intergalaktik/ulx4m-ls/pic/ULX4M-LD_bottom_v001.png

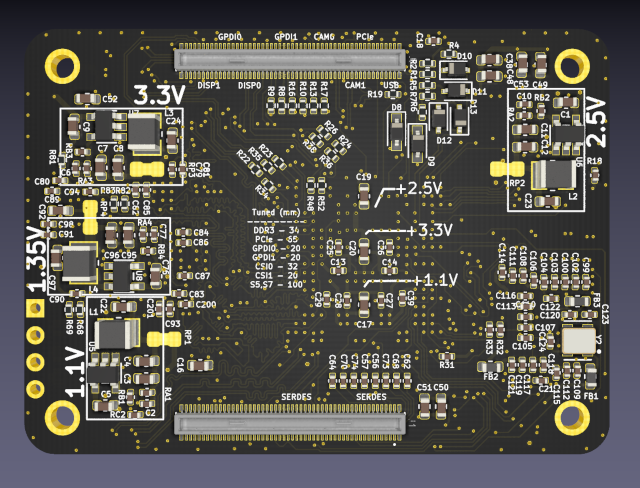
pic/ULX4M-LD_bottom_v001.png
