intergalaktik/ulx4m-ls/pic/ULX4M-LS_top_v003.png

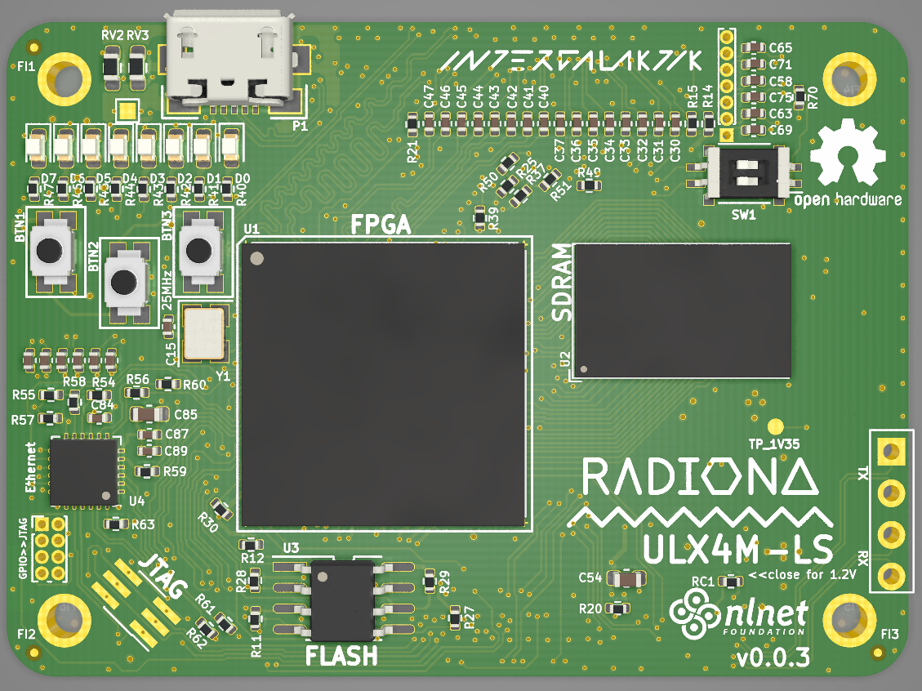
pic/ULX4M-LS_top_v003.png
