intergalaktik/ulx4m-ls/pic/ulx4m.png

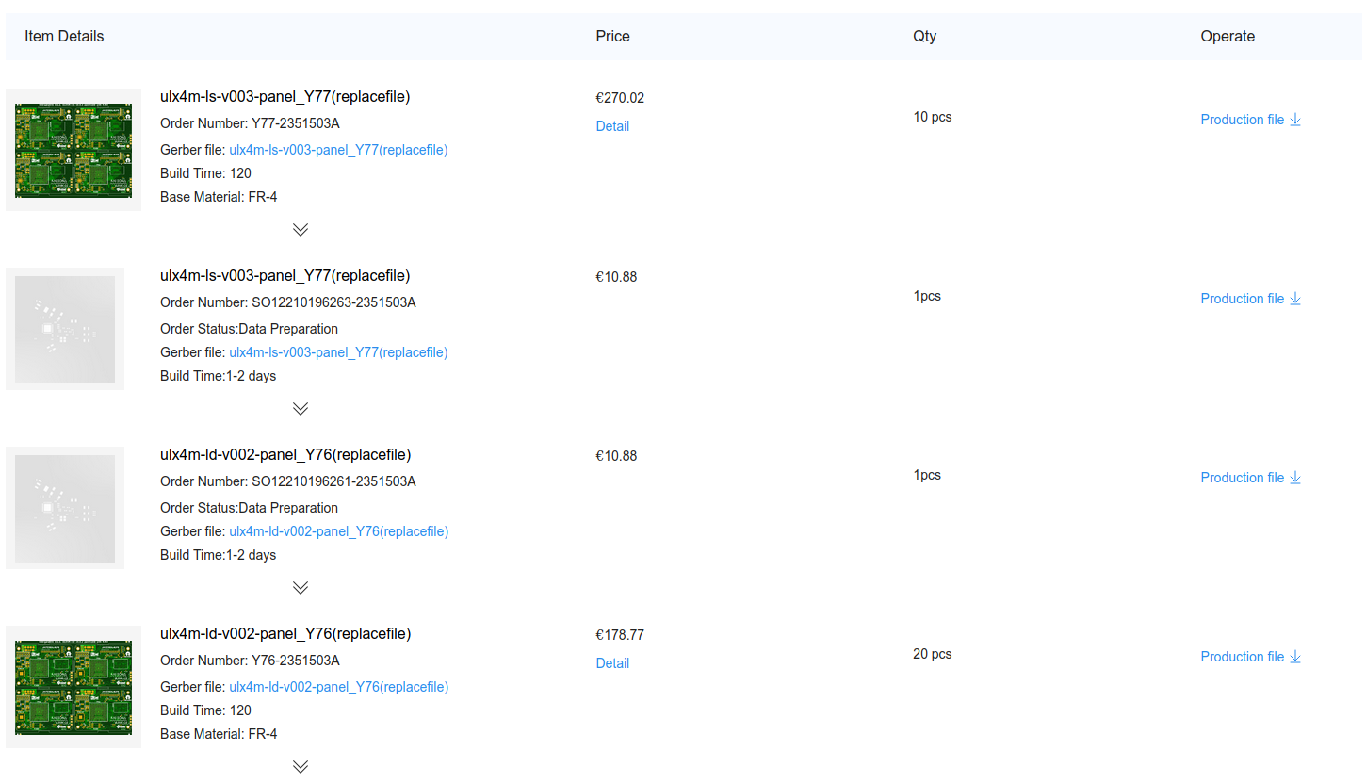
pic/ulx4m.png
