intergalaktik/ulx4m-ls/pic/ulx4m_ld_panel.png

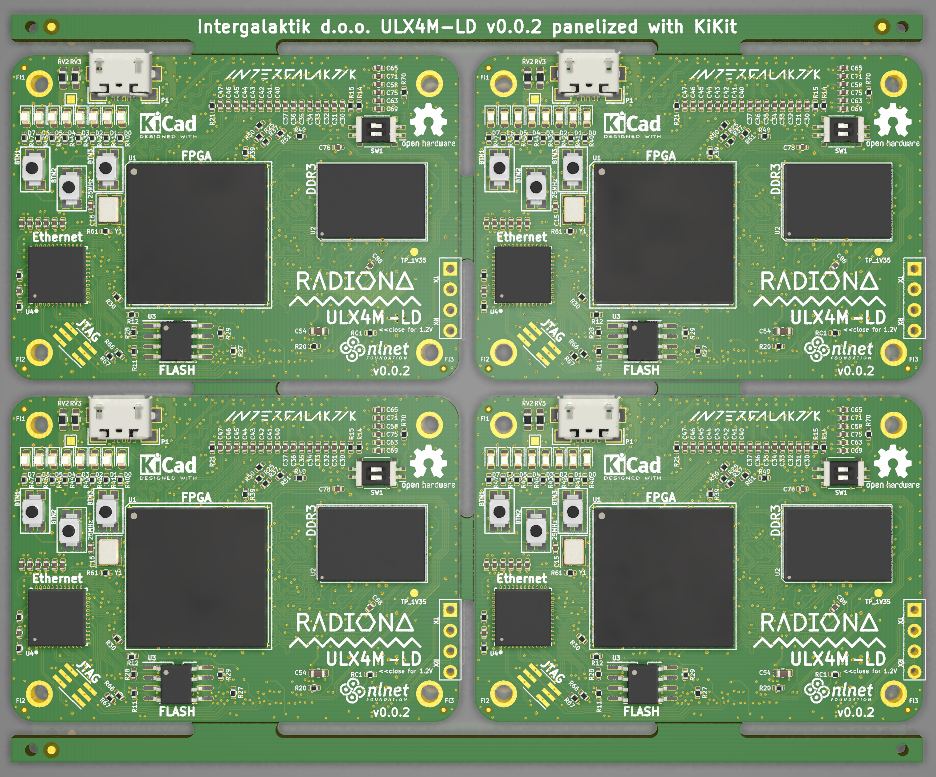
pic/ulx4m_ld_panel.png
