intergalaktik/ulx4m-ls/blinkey.kicad_sch

## KiCad design blinkey.kicad_sch (2025-04-09)

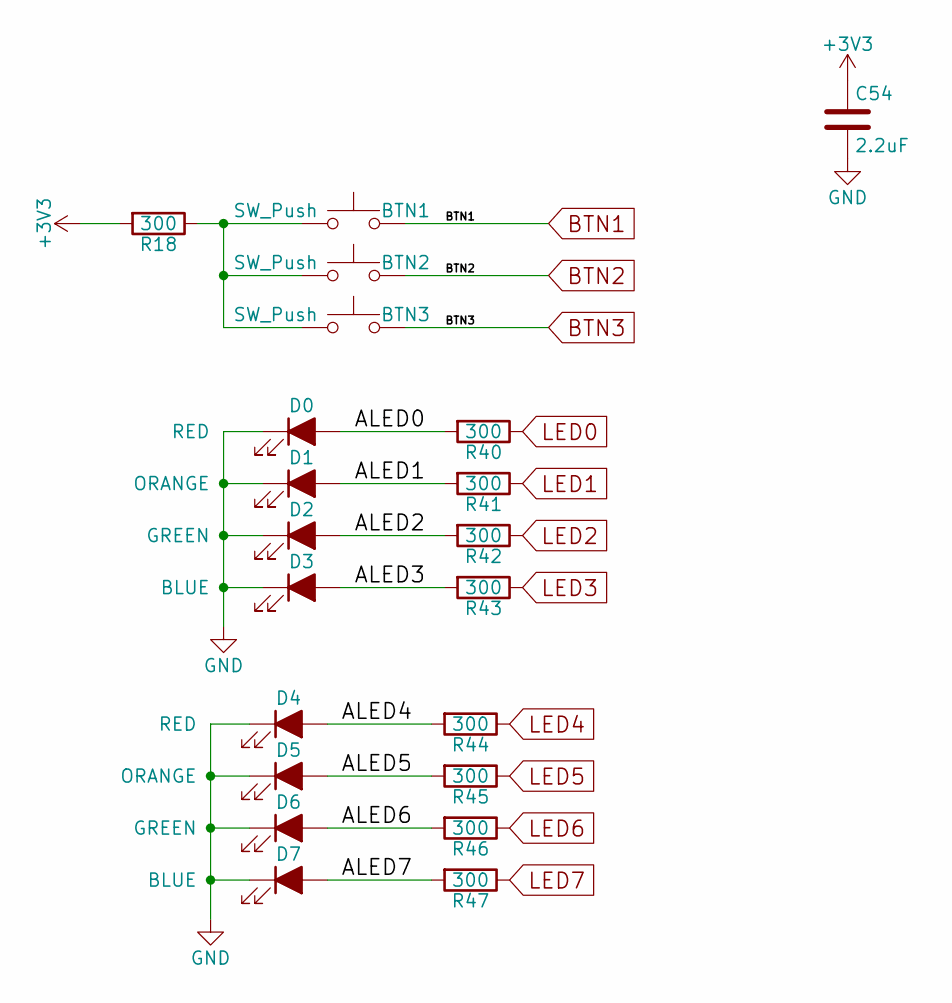
[picture p39: schematic blinkey.kicad_sch]

Parts:
BTN1, BTN2, BTN3: SW_Push; Switch_EVPAA
C54: 2.2uF; C_0603_1608Metric; MPN CC0805MRX5R6BB225
D0, D4: RED; LED_0603_1608Metric; MPN LTST-C170KRKT; Mouser 859-LTST-C170KRKT
D1, D5: ORANGE; LED_0603_1608Metric; MPN LTST-C170KFKT; Mouser 859-LTST-C170KFKT
D2, D6: GREEN; LED_0603_1608Metric; MPN LTST-C170TGKT; Mouser 859-LTST-C170TGKT
D3, D7: BLUE; LED_0603_1608Metric; MPN LTST-C170TBKT; Mouser 859-LTST-C170TBKT
R18, R40, R41, R42, R43, R44, R45, R46, R47: 300; R_0402_1005Metric

Connections:
+3V3: C54.1, R18.2
ALED0: D0.2 (A), R40.2
ALED1: D1.2 (A), R41.2
ALED2: D2.2 (A), R42.2
ALED3: D3.2 (A), R43.2
ALED4: D4.2 (A), R44.2
ALED5: D5.2 (A), R45.2
ALED6: D6.2 (A), R46.2
ALED7: D7.2 (A), R47.2
BTN1: BTN1.2
BTN2: BTN2.2
BTN3: BTN3.2
GND: C54.2, D0.1 (K), D1.1 (K), D2.1 (K), D3.1 (K), D4.1 (K), D5.1 (K), D6.1 (K), D7.1 (K)
LED0: R40.1
LED1: R41.1
LED2: R42.1
LED3: R43.1
LED4: R44.1
LED5: R45.1
LED6: R46.1
LED7: R47.1
unnamed: BTN1.1, BTN2.1, BTN3.1, R18.1
