intergalaktik/ulx4m-ls/ddr3.kicad_sch

## KiCad design ddr3.kicad_sch (2025-04-09)

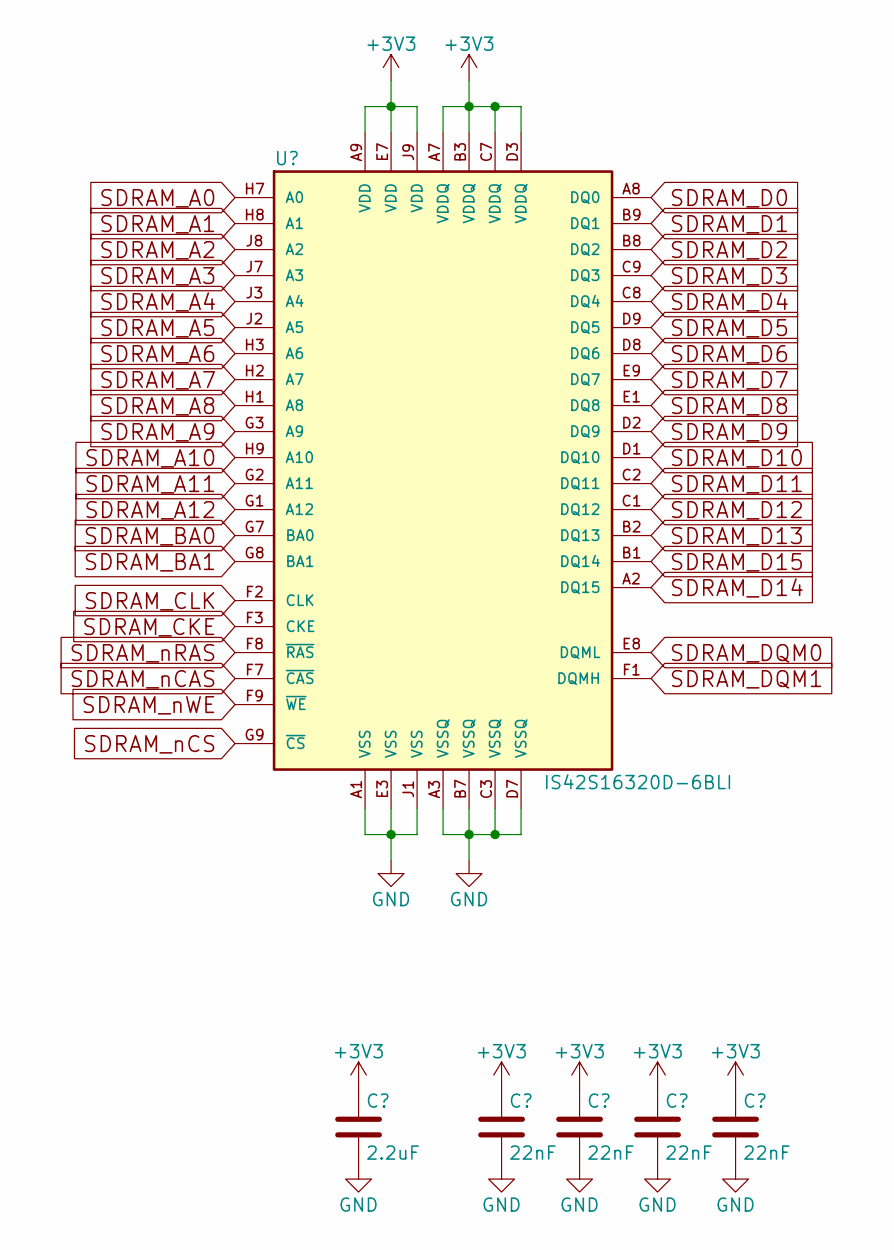
[picture p40: schematic ddr3.kicad_sch]

Parts:
C78: 2.2uF; C_0603_1608Metric
C79, C80, C81: 22nF; C_0402_1005Metric; MPN CX0603MRX7R8BB223
C82: 22nF; C_0603_1608Metric; MPN CX0603MRX7R8BB223
U2: IS42S16320D-6BLI

Connections:
+3V3: C78.1, C79.1, C80.1, C81.1, C82.1, U2.A7 (VDDQ), U2.A9 (VDD), U2.B3 (VDDQ), U2.C7 (VDDQ), U2.D3 (VDDQ), U2.E7 (VDD), U2.J9 (VDD)
GND: C78.2, C79.2, C80.2, C81.2, C82.2, U2.A1 (VSS), U2.A3 (VSSQ), U2.B7 (VSSQ), U2.C3 (VSSQ), U2.D7 (VSSQ), U2.E3 (VSS), U2.J1 (VSS)
SDRAM_A0: U2.H7 (A0)
SDRAM_A1: U2.H8 (A1)
SDRAM_A2: U2.J8 (A2)
SDRAM_A3: U2.J7 (A3)
SDRAM_A4: U2.J3 (A4)
SDRAM_A5: U2.J2 (A5)
SDRAM_A6: U2.H3 (A6)
SDRAM_A7: U2.H2 (A7)
SDRAM_A8: U2.H1 (A8)
SDRAM_A9: U2.G3 (A9)
SDRAM_A10: U2.H9 (A10)
SDRAM_A11: U2.G2 (A11)
SDRAM_A12: U2.G1 (A12)
SDRAM_BA0: U2.G7 (BA0)
SDRAM_BA1: U2.G8 (BA1)
SDRAM_CKE: U2.F3 (CKE)
SDRAM_CLK: U2.F2 (CLK)
SDRAM_D0: U2.A8 (DQ0)
SDRAM_D1: U2.B9 (DQ1)
SDRAM_D2: U2.B8 (DQ2)
SDRAM_D3: U2.C9 (DQ3)
SDRAM_D4: U2.C8 (DQ4)
SDRAM_D5: U2.D9 (DQ5)
SDRAM_D6: U2.D8 (DQ6)
SDRAM_D7: U2.E9 (DQ7)
SDRAM_D8: U2.E1 (DQ8)
SDRAM_D9: U2.D2 (DQ9)
SDRAM_D10: U2.D1 (DQ10)
SDRAM_D11: U2.C2 (DQ11)
SDRAM_D12: U2.C1 (DQ12)
SDRAM_D13: U2.B2 (DQ13)
SDRAM_D14: U2.A2 (DQ15)
SDRAM_D15: U2.B1 (DQ14)
SDRAM_DQM0: U2.E8 (DQML)
SDRAM_DQM1: U2.F1 (DQMH)
SDRAM_nCAS: U2.F7 (~CAS)
SDRAM_nCS: U2.G9 (~CS)
SDRAM_nRAS: U2.F8 (~RAS)
SDRAM_nWE: U2.F9 (~WE)
