intergalaktik/ulx4m-ls/ethernet.kicad_sch

## KiCad design ethernet.kicad_sch (2025-04-09)

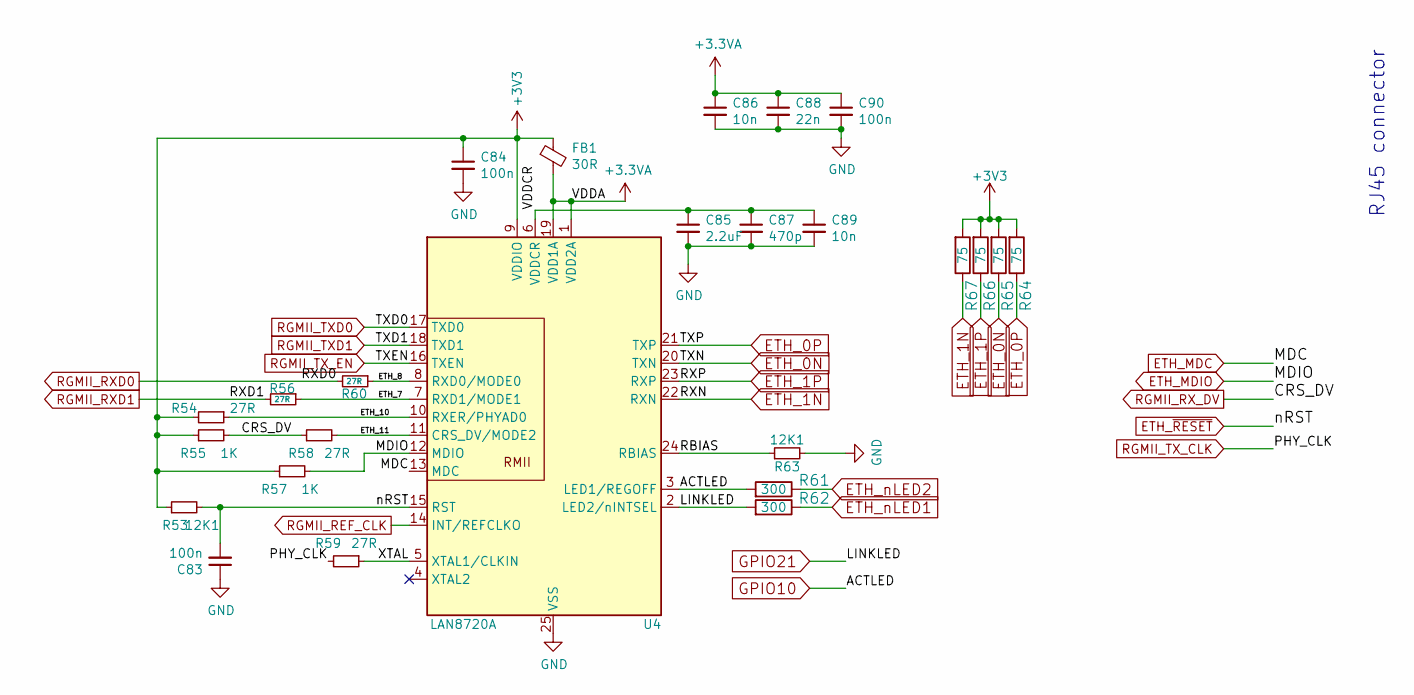
[picture p41: schematic ethernet.kicad_sch]

Parts:
C83, C84, C90: 100n; C_0402_1005Metric
C85: 2.2uF; C_0603_1608Metric
C86, C89: 10n; C_0402_1005Metric
C87: 470p; C_0402_1005Metric
C88: 22n; C_0402_1005Metric
FB1: 30R; L_0603_1608Metric
R53, R63: 12K1; R_0402_1005Metric
R54, R56, R58, R59, R60: 27R; R_0402_1005Metric
R55, R57: 1K; R_0402_1005Metric
R61, R62, R64, R65, R66, R67: 300; R_0402_1005Metric; MPN CR0402-FX-1001GLF
U4: LAN8720A; QFN-24-1EP_4x4mm_P0.5mm_EP2.6x2.6mm

Connections:
+3.3VA: C86.1, C88.1, C90.1, FB1.2, U4.1 (VDD2A), U4.19 (VDD1A)
+3V3: C84.1, FB1.1, R53.1, R54.2, R55.1, R57.1, R64.2, R65.2, R66.2, R67.2, U4.9 (VDDIO)
ETH_0N: R65.1, U4.20 (TXN)
ETH_0P: R64.1, U4.21 (TXP)
ETH_1N: R67.1, U4.22 (RXN)
ETH_1P: R66.1, U4.23 (RXP)
ETH_7: R56.1, U4.7 (RXD1/MODE1)
ETH_8: R60.1, U4.8 (RXD0/MODE0)
ETH_10: R54.1, U4.10 (RXER/PHYAD0)
ETH_11: R58.2, U4.11 (CRS_DV/MODE2)
ETH_MDC: U4.13 (MDC)
ETH_MDIO: R57.2, U4.12 (MDIO)
ETH_nLED1: R62.1
ETH_nLED2: R61.1
ETH_~RESET: C83.2, R53.2, U4.15 (RST)
GND: C83.1, C84.2, C85.2, C86.2, C87.2, C88.2, C89.2, C90.2, R63.2, U4.25 (VSS)
GPIO10: R61.2, U4.3 (LED1/REGOFF)
GPIO21: R62.2, U4.2 (LED2/nINTSEL)
RBIAS: R63.1, U4.24 (RBIAS)
RGMII_REF_CLK: U4.14 (INT/REFCLKO)
RGMII_RXD0: R60.2
RGMII_RXD1: R56.2
RGMII_RX_DV: R55.2, R58.1
RGMII_TXD0: U4.17 (TXD0)
RGMII_TXD1: U4.18 (TXD1)
RGMII_TX_CLK: R59.2
RGMII_TX_EN: U4.16 (TXEN)
VDDCR: C85.1, C87.1, C89.1, U4.6 (VDDCR)
XTAL: R59.1, U4.5 (XTAL1/CLKIN)

Notes on the sheet:
RJ45 connector
