intergalaktik/ulx4m-ls/flash.kicad_sch

## KiCad design flash.kicad_sch (2025-04-09)

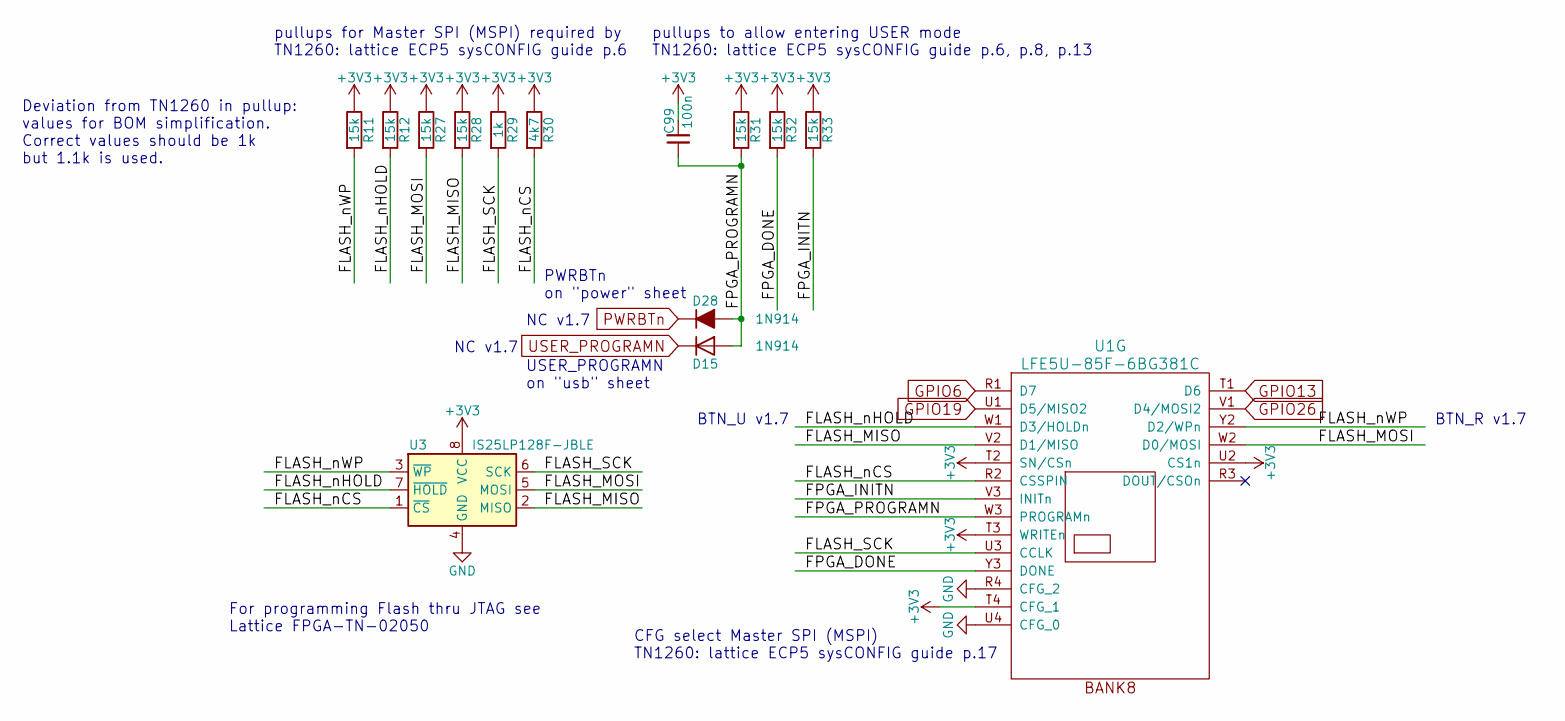
[picture p42: schematic flash.kicad_sch]

Parts:
C99: 100n; C_0402_1005Metric
D15: 1N914; D_SOD-323
D28: 1N914; D_SOD-323; Digike_y 1N4148WXTPMSCT-ND
R11: 15k; R_0402_1005Metric; MPN RC0603FR-0710KL; Mouser 603-RC0603FR-0710KL
R12, R27, R28, R31, R32, R33: 15k; R_0402_1005Metric
R29: 1k; R_0402_1005Metric
R30: 4k7; R_0402_1005Metric; MPN AC0603FR-104K7L
U1: LFE5U-85F-6BG381C; BGA-381_pitch0.8mm_dia0.4mm; MPN LFE5U-85F-6BG381C; Digike_y2 220-2071-ND
U3: IS25LP128F-JBLE; SOA008-150-208mil; MPN IS25LP128F-JBLE; Mouser 727-S25FL128LAMFV013

Connections:
+3V3: C99.2, R11.1, R12.1, R27.1, R28.1, R29.1, R30.1, R31.1, R32.1, R33.1, U1.T2 (SN/CSn), U1.T3 (WRITEn), U1.T4 (CFG_1), U1.U2 (CS1n), U3.8 (VCC)
FLASH_MISO: R28.2, U1.V2 (D1/MISO), U3.2 (MISO)
FLASH_MOSI: R27.2, U1.W2 (D0/MOSI), U3.5 (MOSI)
FLASH_SCK: R29.2, U1.U3 (CCLK), U3.6 (SCK)
FLASH_nCS: R30.2, U1.R2 (CSSPIN), U3.1 (~CS)
FLASH_nHOLD: R12.2, U1.W1 (D3/HOLDn), U3.7 (~HOLD)
FLASH_nWP: R11.2, U1.Y2 (D2/WPn), U3.3 (~WP)
FPGA_DONE: R32.2, U1.Y3 (DONE)
FPGA_INITN: R33.2, U1.V3 (INITn)
FPGA_PROGRAMN: C99.1, D15.2 (A), D28.2 (A), R31.2, U1.W3 (PROGRAMn)
GND: U1.R4 (CFG_2), U1.U4 (CFG_0), U3.4 (GND)
GPIO6: U1.R1 (D7)
GPIO13: U1.T1 (D6)
GPIO19: U1.U1 (D5/MISO2)
GPIO26: U1.V1 (D4/MOSI2)
PWRBTn: D28.1 (K)
USER_PROGRAMN: D15.1 (K)

Notes on the sheet:
pullups for Master SPI (MSPI) required by TN1260: lattice ECP5 sysCONFIG guide p.6
USER_PROGRAMN on "usb" sheet
BTN_R v1.7
For programming Flash thru JTAG see Lattice FPGA-TN-02050
CFG select Master SPI (MSPI) TN1260: lattice ECP5 sysCONFIG guide p.17
Deviation from TN1260 in pullup: values for BOM simplification. Correct values should be 1k but 1.1k is used.
BTN_U v1.7
NC v1.7
PWRBTn on "power" sheet
pullups to allow entering USER mode TN1260: lattice ECP5 sysCONFIG guide p.6, p.8, p.13
