intergalaktik/ulx4m-ls/gpdi.kicad_sch

## KiCad design gpdi.kicad_sch (2025-04-09)

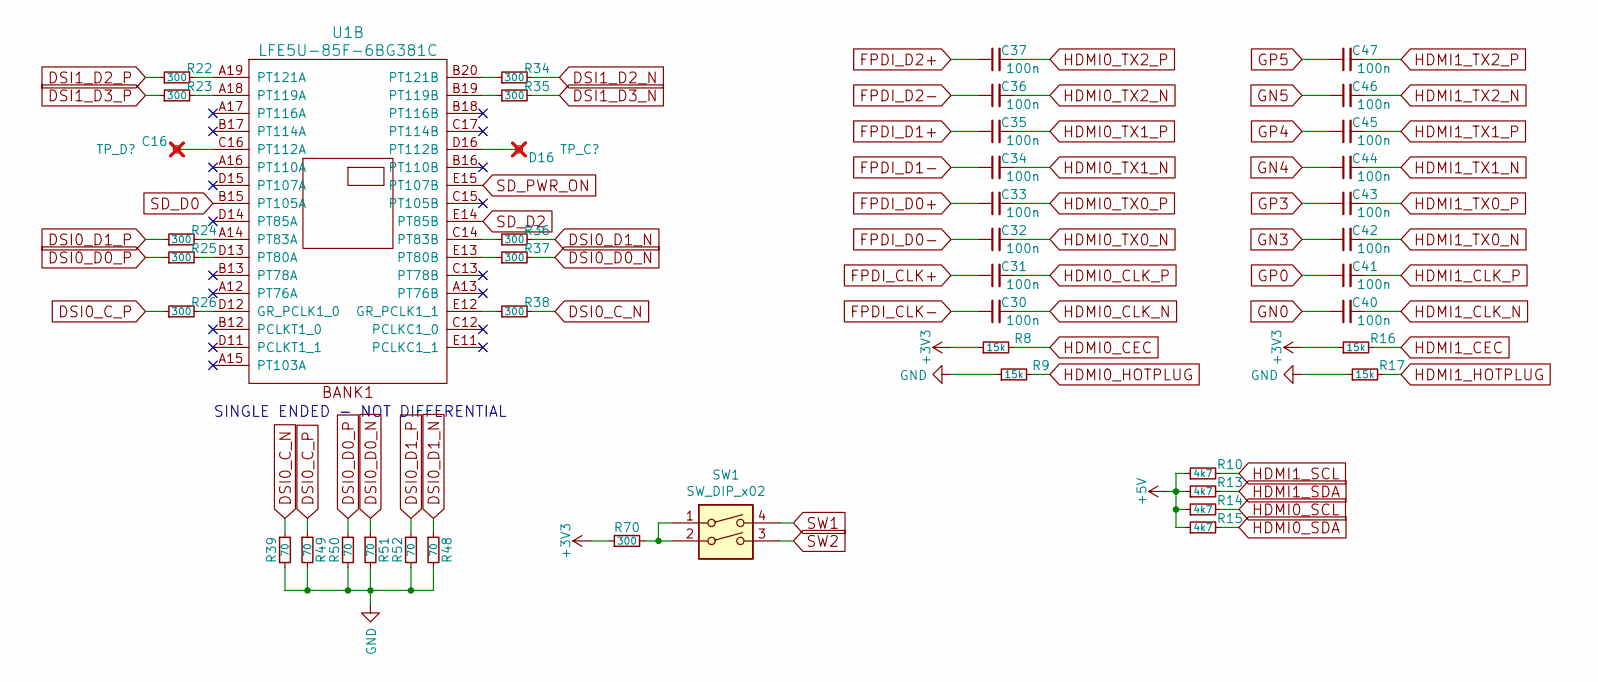
[picture p43: schematic gpdi.kicad_sch]

Parts:
C30, C31, C32, C33, C34, C35, C36, C37, C40, C41, C42, C43, C44, C45, C46, C47: 100n; C_0402_1005Metric
R8, R9, R16, R17: 15k; R_0402_1005Metric
R10, R13, R14, R15: 4k7; R_0402_1005Metric
R22, R23, R24, R25, R26, R34, R35, R36, R37, R38, R70: 300; R_0402_1005Metric
R39, R48, R49, R50, R51, R52: 70; R_0402_1005Metric
SW1: SW_DIP_x02; SW_DIP_SPSTx02_Slide_Copal_CVS-02xB_W5.9mm_P1mm
TP_C16: C16; Testpoint_smd_1mm; not fitted
TP_D16: D16; Testpoint_smd_1mm; not fitted
U1: LFE5U-85F-6BG381C; BGA-381_pitch0.8mm_dia0.4mm; MPN LFE5U-85F-6BG381C; Mouser_URL www.mouser.com

Connections:
+3V3: R8.1, R16.1, R70.1
+5V: R10.1, R13.1, R14.1, R15.1
DSI0_C_N: R38.2, R39.1
DSI0_C_P: R26.1, R49.1
DSI0_D0_N: R37.2, R51.1
DSI0_D0_P: R25.1, R50.1
DSI0_D1_N: R36.2, R48.1
DSI0_D1_P: R24.1, R52.1
DSI1_D2_N: R34.2
DSI1_D2_P: R22.1
DSI1_D3_N: R35.2
DSI1_D3_P: R23.1
FPDI_CLK+: C31.1
FPDI_CLK-: C30.1
FPDI_D0+: C33.1
FPDI_D0-: C32.1
FPDI_D1+: C35.1
FPDI_D1-: C34.1
FPDI_D2+: C37.1
FPDI_D2-: C36.1
GN0: C40.1
GN3: C42.1
GN4: C44.1
GN5: C46.1
GND: R9.1, R17.1, R39.2, R48.2, R49.2, R50.2, R51.2, R52.2
GP0: C41.1
GP3: C43.1
GP4: C45.1
GP5: C47.1
HDMI0_CEC: R8.2
HDMI0_CLK_N: C30.2
HDMI0_CLK_P: C31.2
HDMI0_HOTPLUG: R9.2
HDMI0_SCL: R14.2
HDMI0_SDA: R15.2
HDMI0_TX0_N: C32.2
HDMI0_TX0_P: C33.2
HDMI0_TX1_N: C34.2
HDMI0_TX1_P: C35.2
HDMI0_TX2_N: C36.2
HDMI0_TX2_P: C37.2
HDMI1_CEC: R16.2
HDMI1_CLK_N: C40.2
HDMI1_CLK_P: C41.2
HDMI1_HOTPLUG: R17.2
HDMI1_SCL: R10.2
HDMI1_SDA: R13.2
HDMI1_TX0_N: C42.2
HDMI1_TX0_P: C43.2
HDMI1_TX1_N: C44.2
HDMI1_TX1_P: C45.2
HDMI1_TX2_N: C46.2
HDMI1_TX2_P: C47.2
unnamed: R22.2, U1.A19 (PT121A)
unnamed: R23.2, U1.A18 (PT119A)
unnamed: R24.2, U1.A14 (PT83A)
unnamed: R25.2, U1.D13 (PT80A)
unnamed: R26.2, U1.D12 (GR_PCLK1_0)
unnamed: R34.1, U1.B20 (PT121B)
unnamed: R35.1, U1.B19 (PT119B)
unnamed: R36.1, U1.C14 (PT83B)
unnamed: R37.1, U1.E13 (PT80B)
unnamed: R38.1, U1.E12 (GR_PCLK1_1)
unnamed: R70.2, SW1.1, SW1.2
unnamed: TP_C16.1, U1.C16 (PT112A)
unnamed: TP_D16.1, U1.D16 (PT112B)
SD_D0: U1.B15 (PT105A)
SD_D2: U1.E14 (PT85B)
SD_PWR_ON: U1.E15 (PT107B)
SW1: SW1.4
SW2: SW1.3

Notes on the sheet:
SINGLE ENDED - NOT DIFFERENTIAL
