intergalaktik/ulx4m-ls/ram.kicad_sch

## KiCad design ram.kicad_sch (2025-04-09)

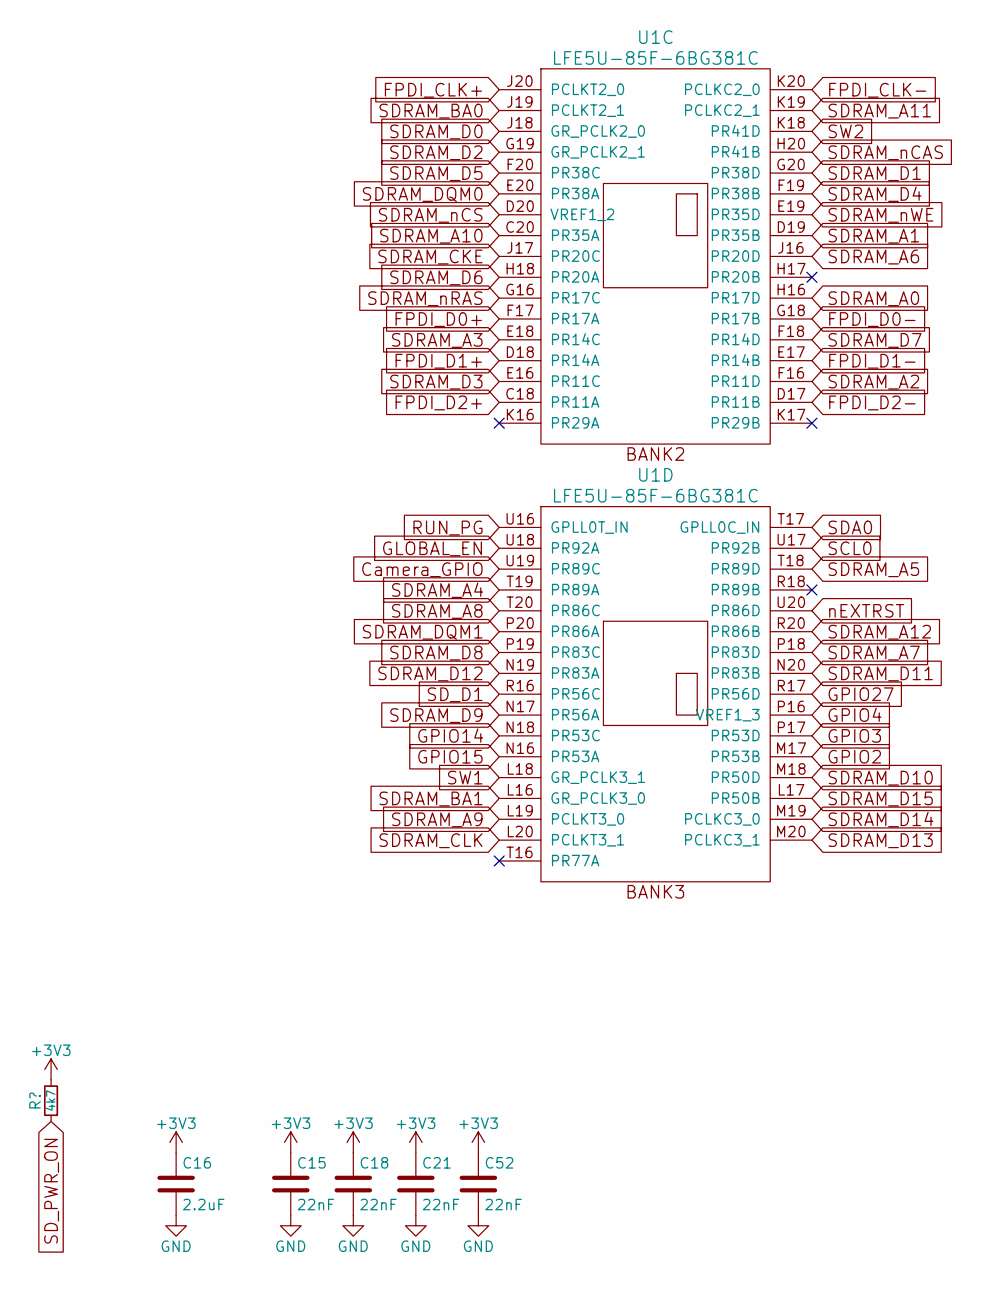
[picture p46: schematic ram.kicad_sch]

Parts:
C15, C18, C21: 22nF; C_0402_1005Metric; MPN CX0603MRX7R8BB223
C16: 2.2uF; C_0603_1608Metric
C52: 22nF; C_0603_1608Metric; MPN CX0603MRX7R8BB223
R20: 4k7; R_0402_1005Metric
U1: LFE5U-85F-6BG381C; BGA-381_pitch0.8mm_dia0.4mm; MPN LFE5U-85F-6BG381C; Digike_y2 220-2071-ND

Connections:
+3V3: C15.1, C16.1, C18.1, C21.1, C52.1, R20.2
Camera_GPIO: U1.U19 (PR89C)
FPDI_CLK+: U1.J20 (PCLKT2_0)
FPDI_CLK-: U1.K20 (PCLKC2_0)
FPDI_D0+: U1.F17 (PR17A)
FPDI_D0-: U1.G18 (PR17B)
FPDI_D1+: U1.D18 (PR14A)
FPDI_D1-: U1.E17 (PR14B)
FPDI_D2+: U1.C18 (PR11A)
FPDI_D2-: U1.D17 (PR11B)
GLOBAL_EN: U1.U18 (PR92A)
GND: C15.2, C16.2, C18.2, C21.2, C52.2
GPIO2: U1.M17 (PR53B)
GPIO3: U1.P17 (PR53D)
GPIO4: U1.P16 (VREF1_3)
GPIO14: U1.N18 (PR53C)
GPIO15: U1.N16 (PR53A)
GPIO27: U1.R17 (PR56D)
RUN_PG: U1.U16 (GPLL0T_IN)
SCL0: U1.U17 (PR92B)
SDA0: U1.T17 (GPLL0C_IN)
SDRAM_A0: U1.H16 (PR17D)
SDRAM_A1: U1.D19 (PR35B)
SDRAM_A2: U1.F16 (PR11D)
SDRAM_A3: U1.E18 (PR14C)
SDRAM_A4: U1.T19 (PR89A)
SDRAM_A5: U1.T18 (PR89D)
SDRAM_A6: U1.J16 (PR20D)
SDRAM_A7: U1.P18 (PR83D)
SDRAM_A8: U1.T20 (PR86C)
SDRAM_A9: U1.L19 (PCLKT3_0)
SDRAM_A10: U1.C20 (PR35A)
SDRAM_A11: U1.K19 (PCLKC2_1)
SDRAM_A12: U1.R20 (PR86B)
SDRAM_BA0: U1.J19 (PCLKT2_1)
SDRAM_BA1: U1.L16 (GR_PCLK3_0)
SDRAM_CKE: U1.J17 (PR20C)
SDRAM_CLK: U1.L20 (PCLKT3_1)
SDRAM_D0: U1.J18 (GR_PCLK2_0)
SDRAM_D1: U1.G20 (PR38D)
SDRAM_D2: U1.G19 (GR_PCLK2_1)
SDRAM_D3: U1.E16 (PR11C)
SDRAM_D4: U1.F19 (PR38B)
SDRAM_D5: U1.F20 (PR38C)
SDRAM_D6: U1.H18 (PR20A)
SDRAM_D7: U1.F18 (PR14D)
SDRAM_D8: U1.P19 (PR83C)
SDRAM_D9: U1.N17 (PR56A)
SDRAM_D10: U1.M18 (PR50D)
SDRAM_D11: U1.N20 (PR83B)
SDRAM_D12: U1.N19 (PR83A)
SDRAM_D13: U1.M20 (PCLKC3_1)
SDRAM_D14: U1.M19 (PCLKC3_0)
SDRAM_D15: U1.L17 (PR50B)
SDRAM_DQM0: U1.E20 (PR38A)
SDRAM_DQM1: U1.P20 (PR86A)
SDRAM_nCAS: U1.H20 (PR41B)
SDRAM_nCS: U1.D20 (VREF1_2)
SDRAM_nRAS: U1.G16 (PR17C)
SDRAM_nWE: U1.E19 (PR35D)
SD_D1: U1.R16 (PR56C)
SD_PWR_ON: R20.1
SW1: U1.L18 (GR_PCLK3_1)
SW2: U1.K18 (PR41D)
nEXTRST: U1.U20 (PR86D)
