intergalaktik/ulx4m-ls/serdes.kicad_sch

## KiCad design serdes.kicad_sch (2025-04-09)

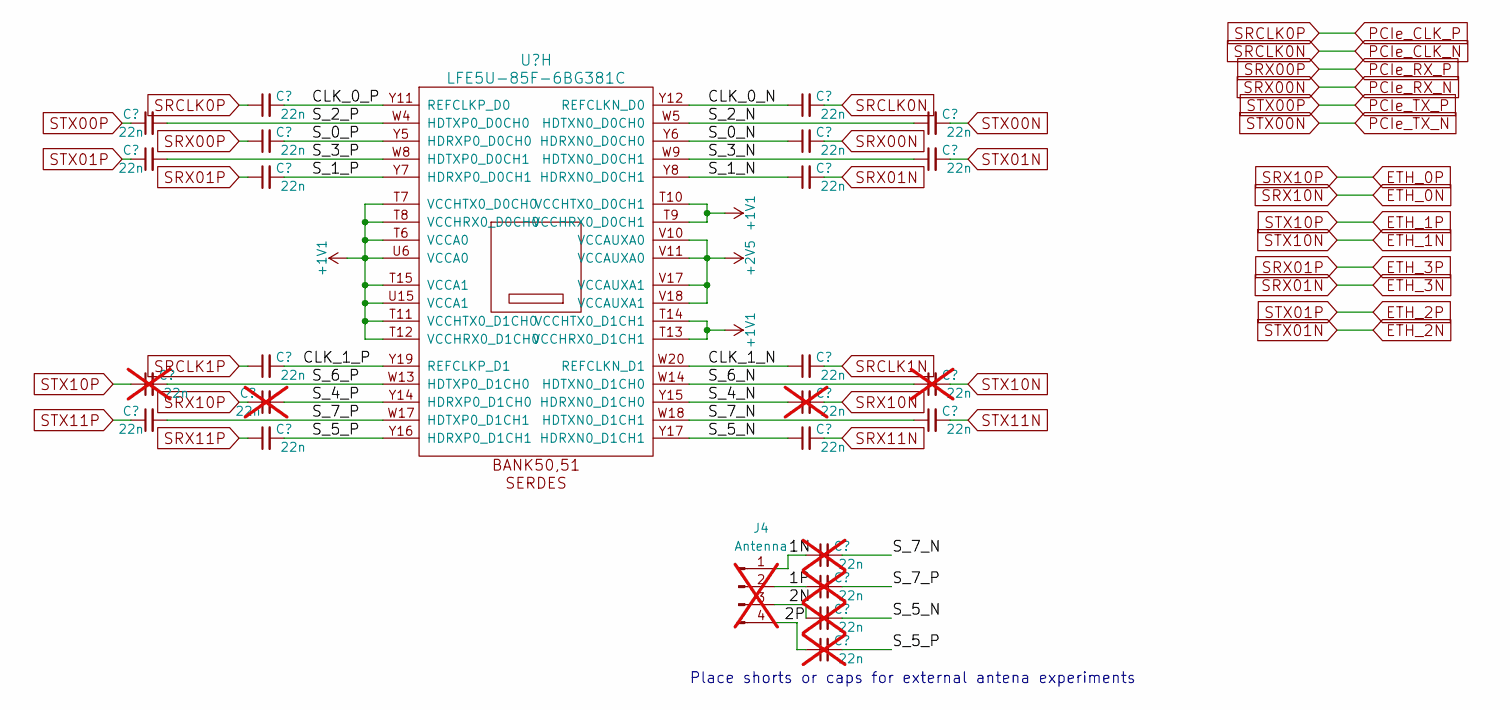
[picture p47: schematic serdes.kicad_sch]

Parts:
C55, C56, C58, C59, C61, C62, C63, C65, C66, C67, C68, C69, C71, C72, C73, C75: 22n; C_0402_1005Metric
C57, C64, C70, C74: 22n; not fitted
C91, C92, C93, C94: 22n; C_0201_0603Metric; not fitted
J4: Antenna; PinHeader_1x04_P2.54mm_Vertical; not fitted
U1: LFE5U-85F-6BG381C; BGA-381_pitch0.8mm_dia0.4mm; MPN LFE5U-85F-6BG381C; Mouser 842-LFE5U85F6BG381C

Connections:
1N: C91.1, J4.1
1P: C92.1, J4.2
2N: C93.1, J4.3
2P: C94.1, J4.4
+1V1: U1.T6 (VCCA0), U1.T7 (VCCHTX0_D0CH0), U1.T8 (VCCHRX0_D0CH0), U1.T9 (VCCHRX0_D0CH1), U1.T10 (VCCHTX0_D0CH1), U1.T11 (VCCHTX0_D1CH0), U1.T12 (VCCHRX0_D1CH0), U1.T13 (VCCHRX0_D1CH1), U1.T14 (VCCHTX0_D1CH1), U1.T15 (VCCA1), U1.U6 (VCCA0), U1.U15 (VCCA1)
+2V5: U1.V10 (VCCAUXA0), U1.V11 (VCCAUXA0), U1.V17 (VCCAUXA1), U1.V18 (VCCAUXA1)
CLK_0_N: C66.1, U1.Y12 (REFCLKN_D0)
CLK_0_P: C59.2, U1.Y11 (REFCLKP_D0)
CLK_1_N: C69.1, U1.W20 (REFCLKN_D1)
CLK_1_P: C63.2, U1.Y19 (REFCLKP_D1)
ETH_0N: C74.2
ETH_0P: C57.1
ETH_1N: C70.2
ETH_1P: C64.1
ETH_2N: C73.2
ETH_2P: C56.1
ETH_3N: C68.2
ETH_3P: C62.1
PCIe_CLK_N: C66.2
PCIe_CLK_P: C59.1
PCIe_RX_N: C67.2
PCIe_RX_P: C61.1
PCIe_TX_N: C72.2
PCIe_TX_P: C55.1
SRCLK1N: C69.2
SRCLK1P: C63.1
SRX11N: C71.2
SRX11P: C65.1
STX11N: C75.2
STX11P: C58.1
S_0_N: C67.1, U1.Y6 (HDRXN0_D0CH0)
S_0_P: C61.2, U1.Y5 (HDRXP0_D0CH0)
S_1_N: C68.1, U1.Y8 (HDRXN0_D0CH1)
S_1_P: C62.2, U1.Y7 (HDRXP0_D0CH1)
S_2_N: C72.1, U1.W5 (HDTXN0_D0CH0)
S_2_P: C55.2, U1.W4 (HDTXP0_D0CH0)
S_3_N: C73.1, U1.W9 (HDTXN0_D0CH1)
S_3_P: C56.2, U1.W8 (HDTXP0_D0CH1)
S_4_N: C74.1, U1.Y15 (HDRXN0_D1CH0)
S_4_P: C57.2, U1.Y14 (HDRXP0_D1CH0)
S_5_N: C71.1, C93.2, U1.Y17 (HDRXN0_D1CH1)
S_5_P: C65.2, C94.2, U1.Y16 (HDRXP0_D1CH1)
S_6_N: C70.1, U1.W14 (HDTXN0_D1CH0)
S_6_P: C64.2, U1.W13 (HDTXP0_D1CH0)
S_7_N: C75.1, C91.2, U1.W18 (HDTXN0_D1CH1)
S_7_P: C58.2, C92.2, U1.W17 (HDTXP0_D1CH1)

Notes on the sheet:
Place shorts or caps for external antena experiments
