intergalaktik/ulx4m-ls/ulx4m.kicad_sch

## KiCad design ulx4m.kicad_sch (2025-04-09)

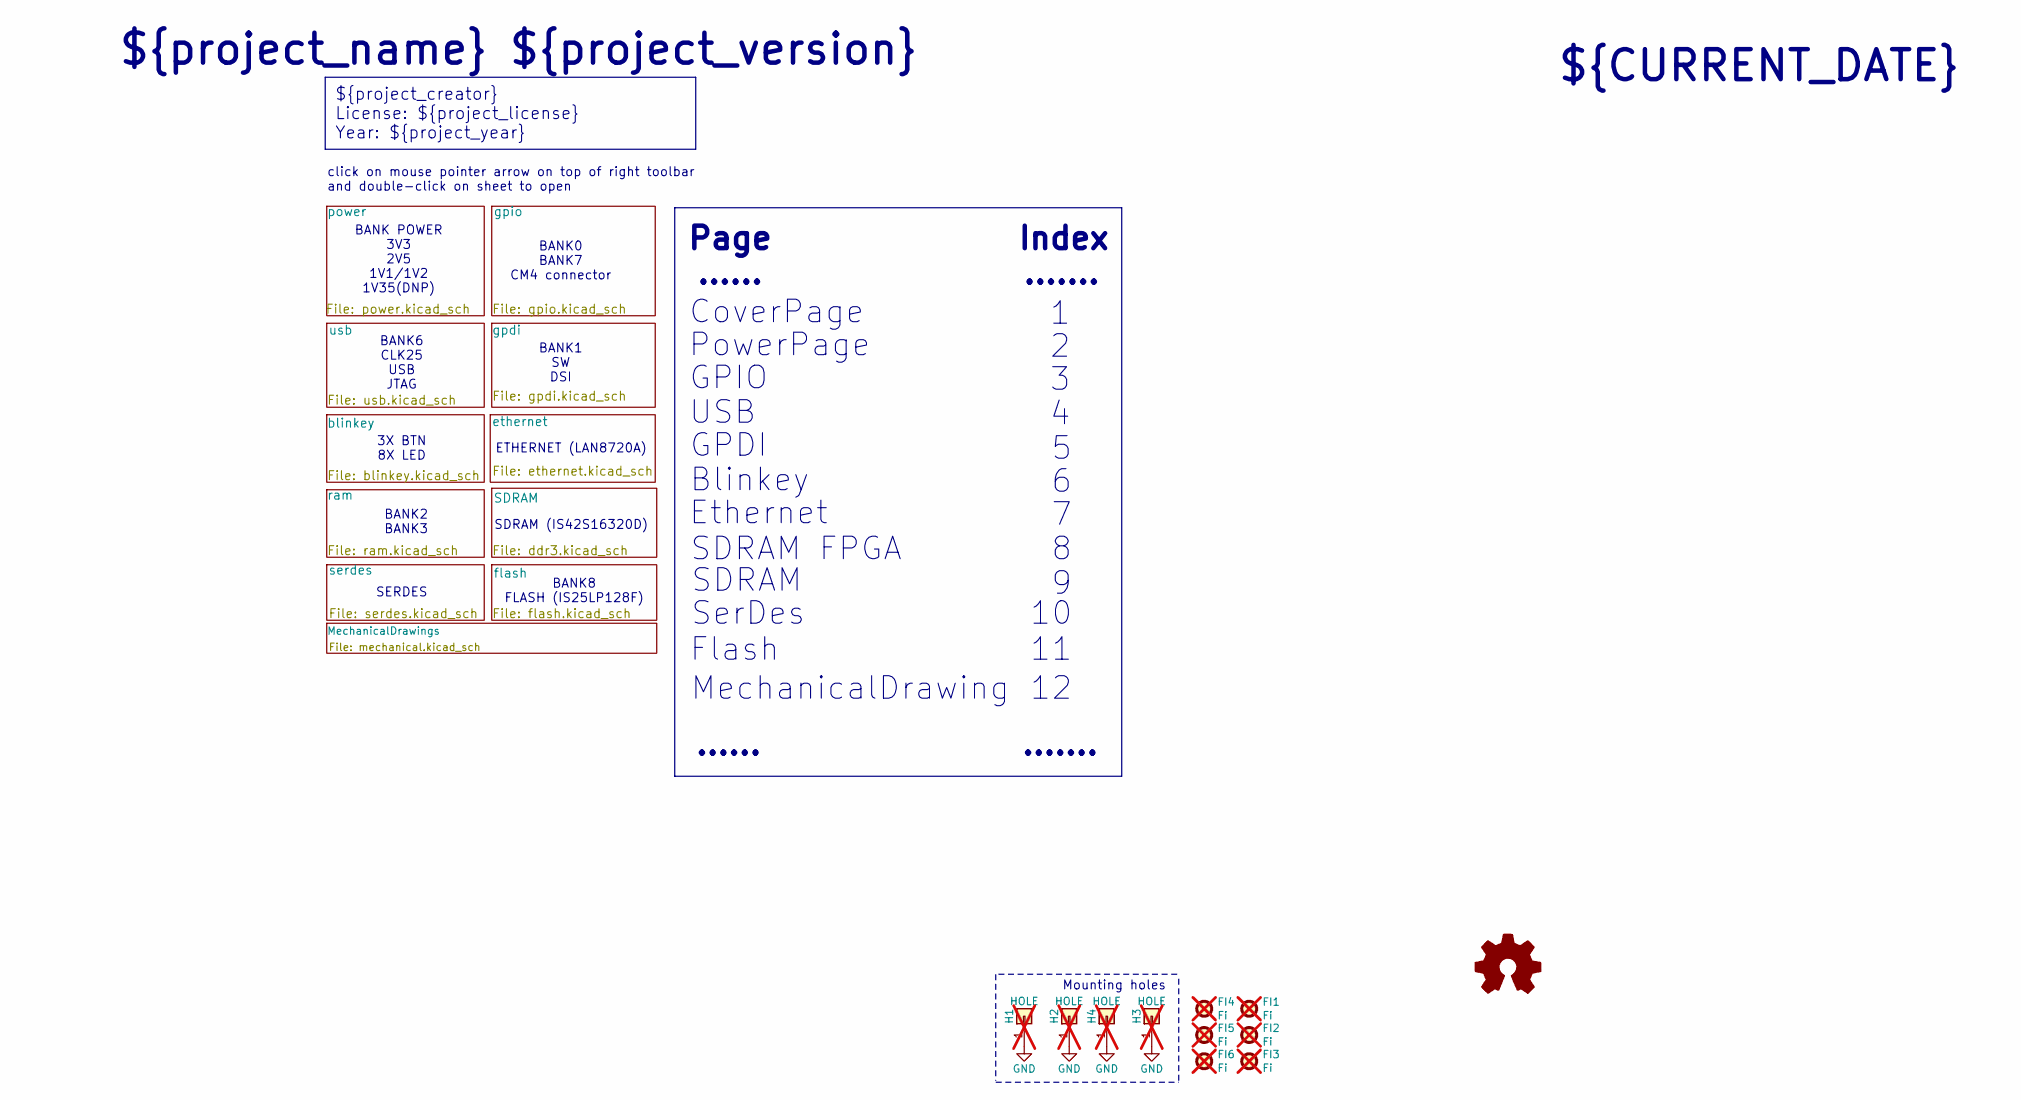
[picture p48: schematic ulx4m.kicad_sch]

Parts:
FI1, FI2, FI3, FI4, FI5, FI6: Fi; Fiducial_0.5mm_Mask1mm; not fitted
H1, H2, H3, H4: HOLE; MountingHole_3.2mm_M3_ISO14580_Pad; not fitted

Connections:
GND: H1.1, H2.1, H3.1, H4.1

Notes on the sheet:
${project_creator} License: ${project_license} Year: ${project_year}
MechanicalDrawing
Page
PowerPage
......
SDRAM (IS42S16320D)
.......
BANK1 SW DSI
3X BTN 8X LED
GPIO
BANK8 FLASH (IS25LP128F)
Flash
BANK POWER 3V3 2V5 1V1/1V2 1V35(DNP)
ETHERNET (LAN8720A)
BANK6 CLK25 USB JTAG
click on mouse pointer arrow on top of right toolbar and double-click on sheet to open
GPDI
SerDes
Blinkey
${project_name} ${project_version}
SDRAM
${CURRENT_DATE}
BANK0 BANK7 CM4 connector
CoverPage
Ethernet
Mounting holes
USB
Index
SERDES
SDRAM FPGA
BANK2 BANK3
